bolidozor/NEC-models/antennas/CAD/QHA-SC.png

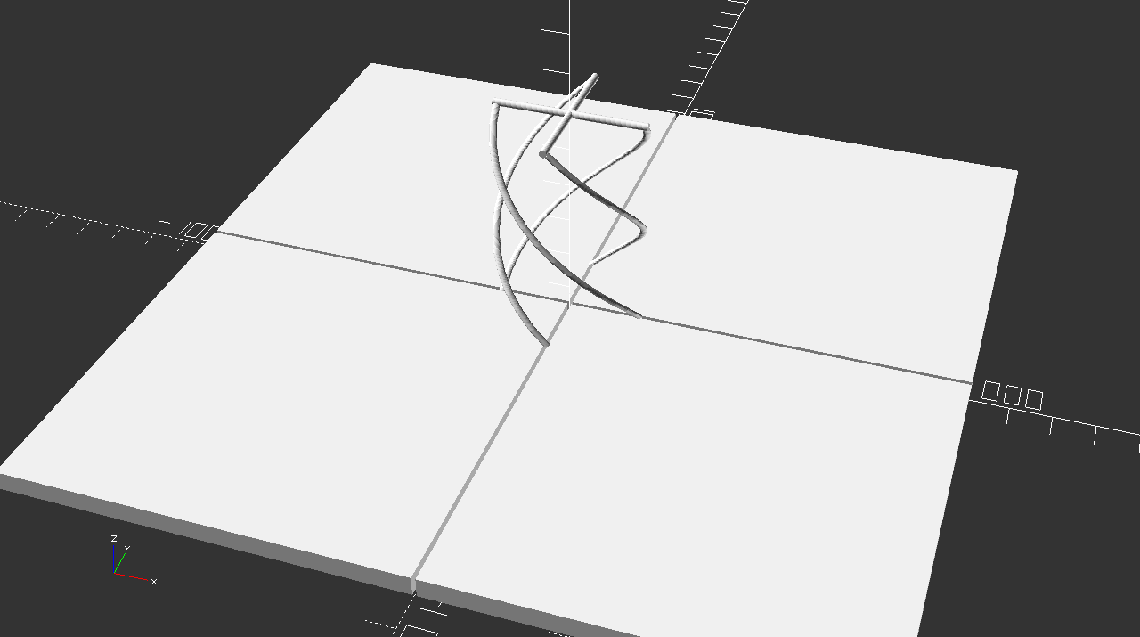
antennas/CAD/QHA-SC.png
