bolidozor/NEC-models/antennas/CAD/QHA-SC_array.png

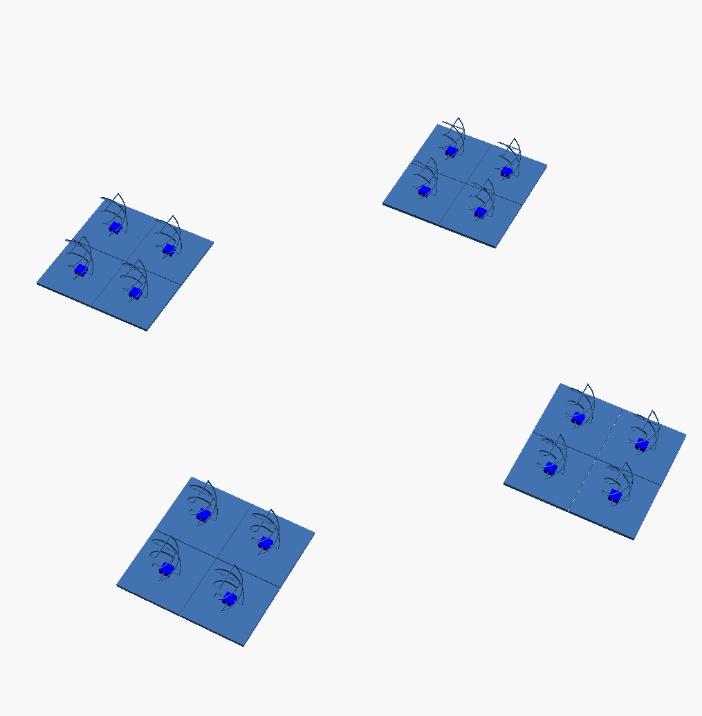
antennas/CAD/QHA-SC_array.png
