bolidozor/NEC-models/DOC/src/img/bolidozor_patch_antenna1.jpg

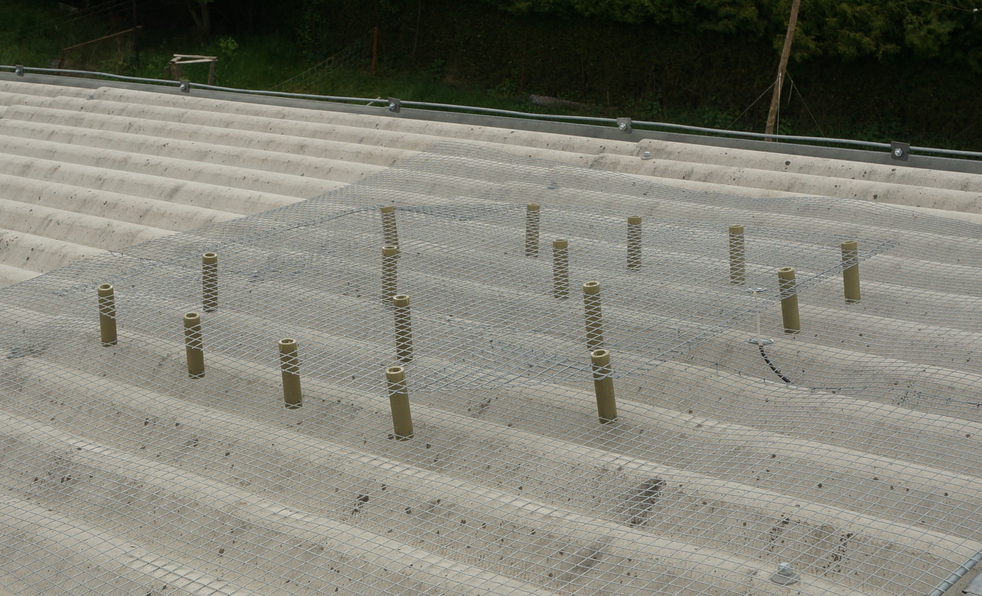
DOC/src/img/bolidozor_patch_antenna1.jpg
